KK153402/ESP32_FamicomRomdumper/hardware/Famicom1.kicad_sch

## KiCad design hardware/Famicom1.kicad_sch (2026-09-27)

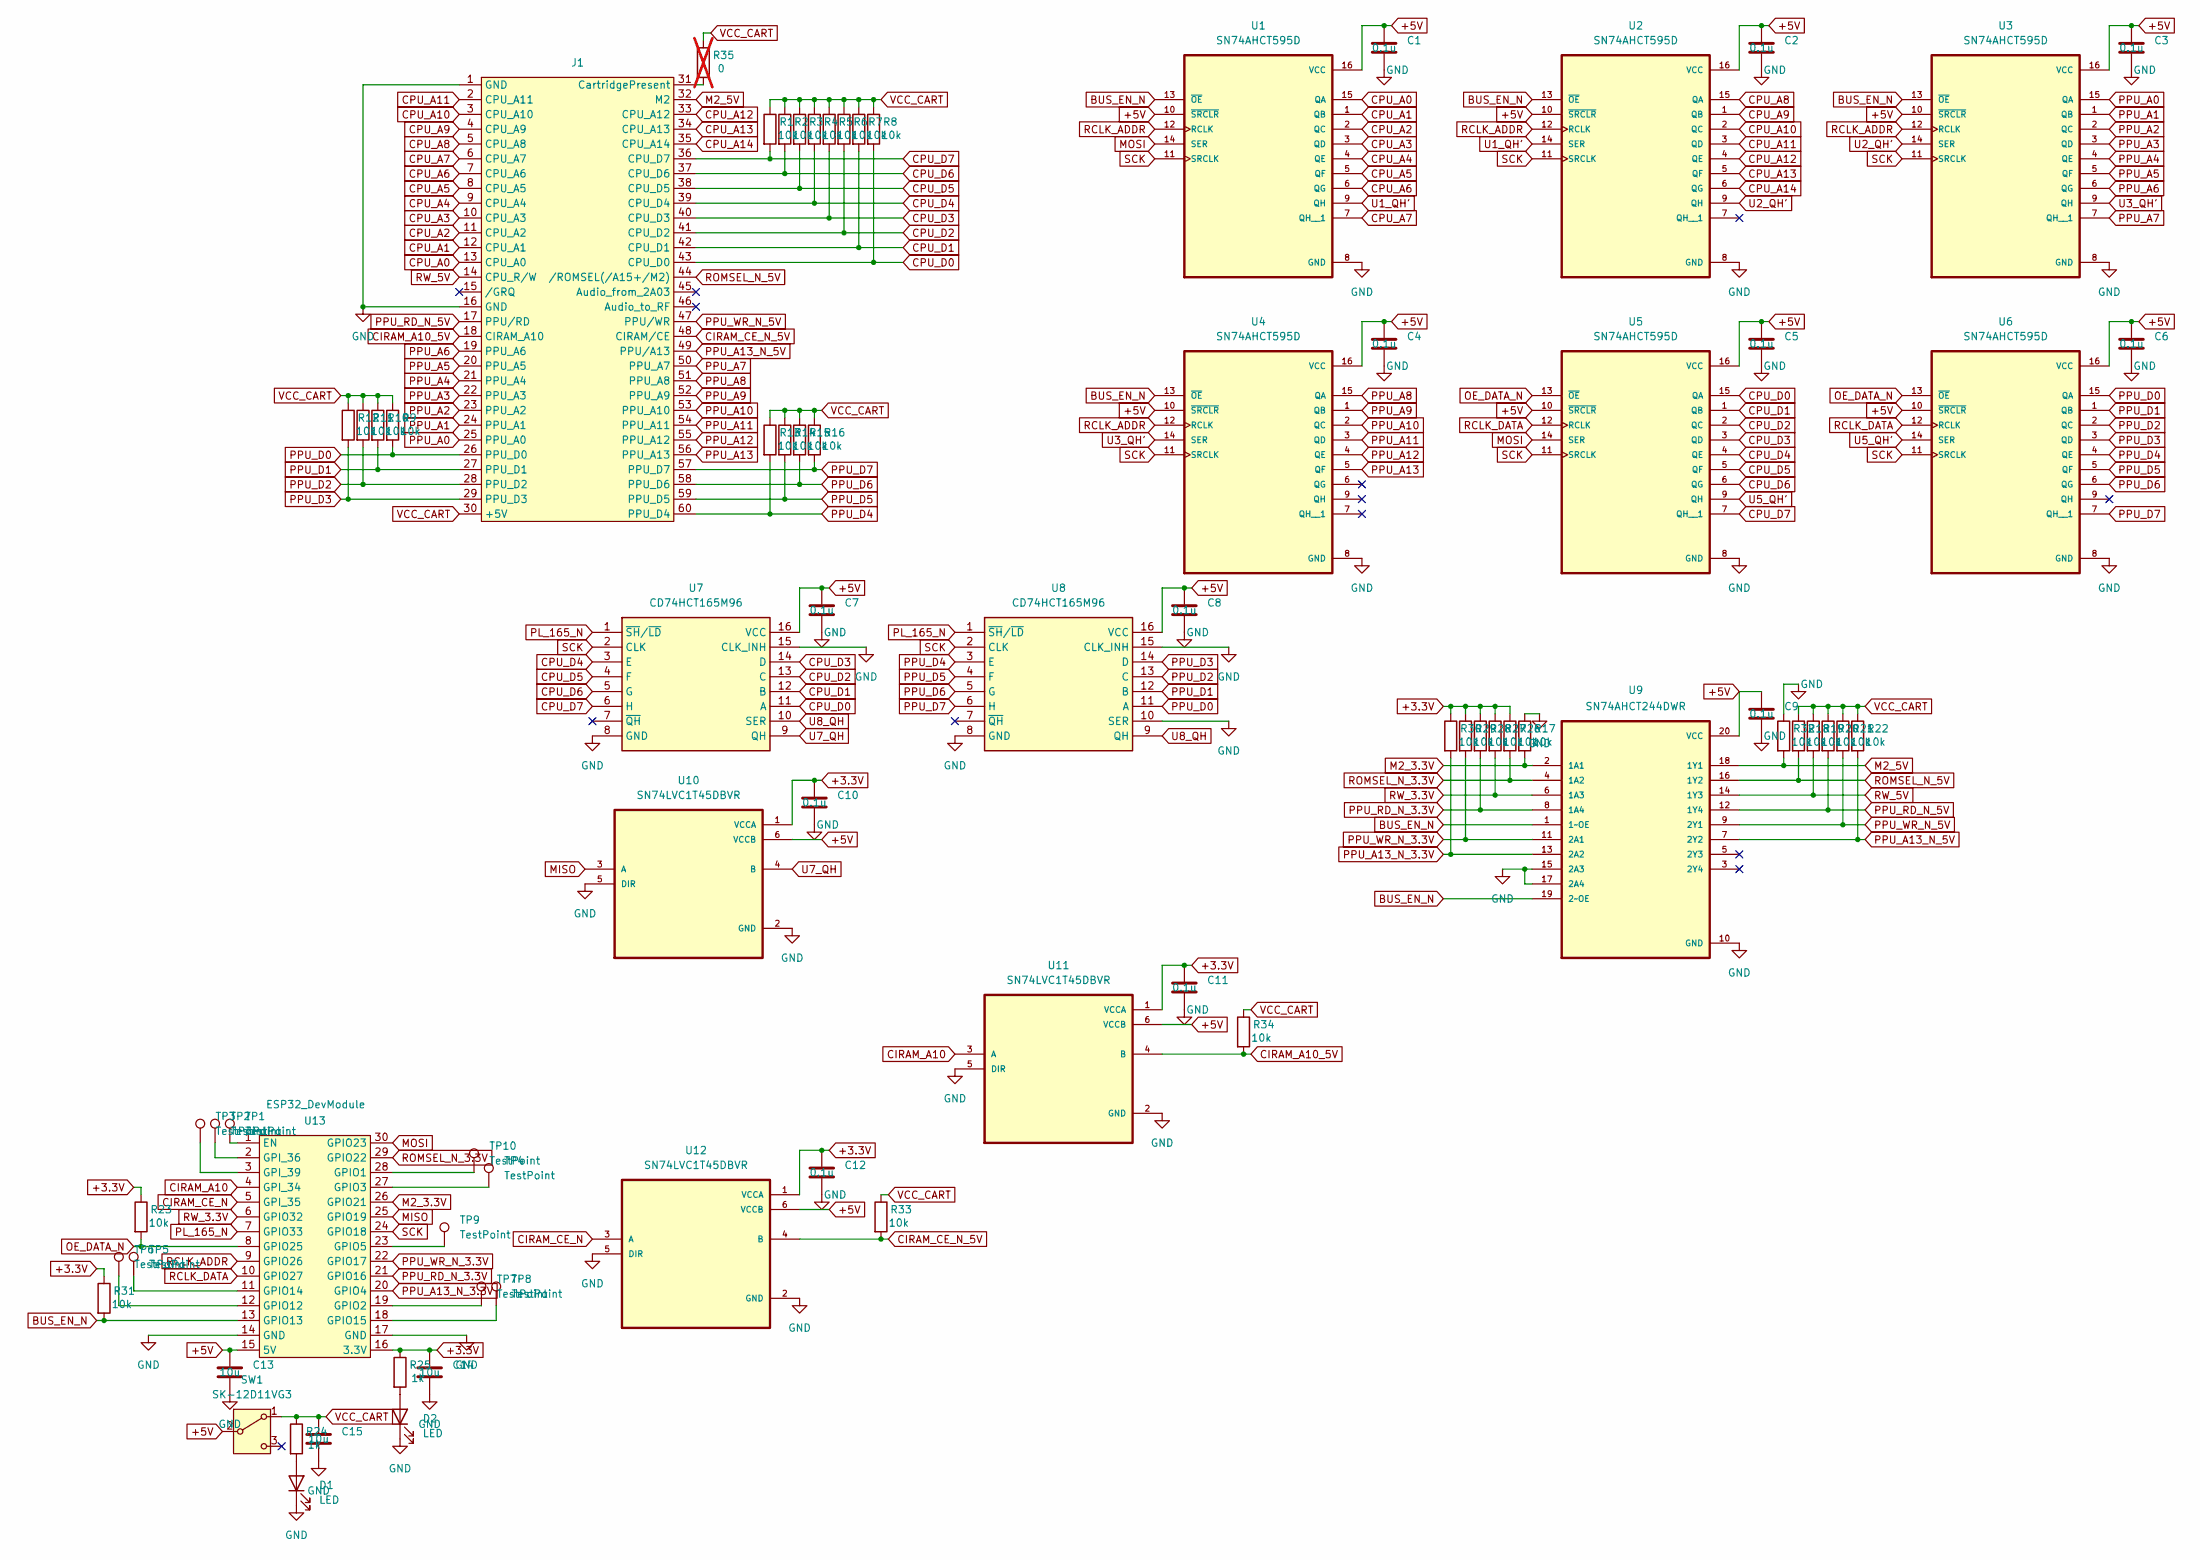
[picture p6: schematic Famicom1.kicad_sch]

Parts:
C1, C2, C3, C4, C5, C6, C7, C8, C9, C10, C11, C12: GRM188F11H104ZA01; C_0603_1608Metric
C13, C14, C15: GRM31CB31H106KA12; C_1206_3216Metric
D1, D2: LED; SML-E12P8WT86
J1: FamilyComputer_60pin
R1, R2, R3, R4, R5, R6, R7, R8, R9, R10, R11, R12, R13, R14, R15, R16, R17, R18, R19, R20, R21, R22, R23, R26, R27, R28, R29, R30, R31, R32, R33, R34: RK73B1JTTD103J; R_0603_1608Metric
R24, R25: RK73B1JTTD102J; R_0603_1608Metric
R35: RK73Z1JTTD; R_0603_1608Metric; not fitted
SW1: SK-12D11VG3
TP1, TP2, TP3, TP4, TP5, TP6, TP7, TP8, TP9, TP10: TestPoint; TestPoint_Pad_2.5x2.5mm
U1, U2, U3, U4, U5, U6: SN74AHCT595D
U7, U8: CD74HCT165M96; Manufacturer_Part_Number CD74HCT165M96; Mouser Part Number 595-CD74HCT165M96
U9: SN74AHCT244DWR
U10, U11, U12: SN74LVC1T45DBVR
U13: ESP32_DevModule

Connections:
+3.3V: C10.1, C11.1, C12.1, C14.1, R23.1, R25.1, R26.1, R27.1, R28.1, R29.1, R30.1, R31.1, U10.1 (VCCA), U11.1 (VCCA), U12.1 (VCCA), U13.16 (3.3V)
+5V: C1.1, C2.1, C3.1, C4.1, C5.1, C6.1, C7.1, C8.1, C9.1, C13.1, SW1.2 (B), U1.10 (~SRCLR), U1.16 (VCC), U2.10 (~SRCLR), U2.16 (VCC), U3.10 (~SRCLR), U3.16 (VCC), U4.10 (~SRCLR), U4.16 (VCC), U5.10 (~SRCLR), U5.16 (VCC), U6.10 (~SRCLR), U6.16 (VCC), U7.16 (VCC), U8.16 (VCC), U9.20 (VCC), U10.6 (VCCB), U11.6 (VCCB), U12.6 (VCCB), U13.15 (5V)
BUS_EN_N: R31.2, U1.13 (~OE), U2.13 (~OE), U3.13 (~OE), U4.13 (~OE), U9.1 (1~OE), U9.19 (2~OE), U13.13 (GPIO13)
CIRAM_A10: U11.3 (A), U13.4 (GPI_34)
CIRAM_A10_5V: J1.18 (CIRAM_A10), R34.2, U11.4 (B)
CIRAM_CE_N: U12.3 (A), U13.5 (GPI_35)
CIRAM_CE_N_5V: J1.48 (CIRAM/CE), R33.2, U12.4 (B)
CPU_A0: J1.13 (CPU_A0), U1.15 (QA)
CPU_A1: J1.12 (CPU_A1), U1.1 (QB)
CPU_A2: J1.11 (CPU_A2), U1.2 (QC)
CPU_A3: J1.10 (CPU_A3), U1.3 (QD)
CPU_A4: J1.9 (CPU_A4), U1.4 (QE)
CPU_A5: J1.8 (CPU_A5), U1.5 (QF)
CPU_A6: J1.7 (CPU_A6), U1.6 (QG)
CPU_A7: J1.6 (CPU_A7), U1.7 (QH__1)
CPU_A8: J1.5 (CPU_A8), U2.15 (QA)
CPU_A9: J1.4 (CPU_A9), U2.1 (QB)
CPU_A10: J1.3 (CPU_A10), U2.2 (QC)
CPU_A11: J1.2 (CPU_A11), U2.3 (QD)
CPU_A12: J1.33 (CPU_A12), U2.4 (QE)
CPU_A13: J1.34 (CPU_A13), U2.5 (QF)
CPU_A14: J1.35 (CPU_A14), U2.6 (QG)
CPU_D0: J1.43 (CPU_D0), R8.2, U5.15 (QA), U7.11 (A)
CPU_D1: J1.42 (CPU_D1), R7.2, U5.1 (QB), U7.12 (B)
CPU_D2: J1.41 (CPU_D2), R6.2, U5.2 (QC), U7.13 (C)
CPU_D3: J1.40 (CPU_D3), R5.2, U5.3 (QD), U7.14 (D)
CPU_D4: J1.39 (CPU_D4), R4.2, U5.4 (QE), U7.3 (E)
CPU_D5: J1.38 (CPU_D5), R3.2, U5.5 (QF), U7.4 (F)
CPU_D6: J1.37 (CPU_D6), R2.2, U5.6 (QG), U7.5 (G)
CPU_D7: J1.36 (CPU_D7), R1.2, U5.7 (QH__1), U7.6 (H)
GND: C1.2, C2.2, C3.2, C4.2, C5.2, C6.2, C7.2, C8.2, C9.2, C10.2, C11.2, C12.2, C13.2, C14.2, C15.2, D1.1 (K), D2.1 (K), J1.1 (GND), J1.16 (GND), R17.1, R32.1, U1.8 (GND), U2.8 (GND), U3.8 (GND), U4.8 (GND), U5.8 (GND), U6.8 (GND), U7.8 (GND), U7.15 (CLK_INH), U8.8 (GND), U8.10 (SER), U8.15 (CLK_INH), U9.10 (GND), U9.15 (2A3), U9.17 (2A4), U10.2 (GND), U10.5 (DIR), U11.2 (GND), U11.5 (DIR), U12.2 (GND), U12.5 (DIR), U13.14 (GND), U13.17 (GND)
M2_3.3V: R17.2, U9.2 (1A1), U13.26 (GPIO21)
M2_5V: J1.32 (M2), R32.2, U9.18 (1Y1)
MISO: U10.3 (A), U13.25 (GPIO19)
MOSI: U1.14 (SER), U5.14 (SER), U13.30 (GPIO23)
unnamed: D1.2 (A), R24.2
unnamed: D2.2 (A), R25.2
unnamed: J1.31 (CartridgePresent), R35.2
unnamed: TP1.1, U13.1 (EN)
unnamed: TP2.1, U13.2 (GPI_36)
unnamed: TP3.1, U13.3 (GPI_39)
unnamed: TP4.1, U13.27 (GPIO3)
unnamed: TP5.1, U13.11 (GPIO14)
unnamed: TP6.1, U13.12 (GPIO12)
unnamed: TP7.1, U13.19 (GPIO2)
unnamed: TP8.1, U13.18 (GPIO15)
unnamed: TP9.1, U13.23 (GPIO5)
unnamed: TP10.1, U13.28 (GPIO1)
OE_DATA_N: R23.2, U5.13 (~OE), U6.13 (~OE), U13.8 (GPIO25)
PL_165_N: U7.1 (~SH/~LD), U8.1 (~SH/~LD), U13.7 (GPIO33)
PPU_A0: J1.25 (PPU_A0), U3.15 (QA)
PPU_A1: J1.24 (PPU_A1), U3.1 (QB)
PPU_A2: J1.23 (PPU_A2), U3.2 (QC)
PPU_A3: J1.22 (PPU_A3), U3.3 (QD)
PPU_A4: J1.21 (PPU_A4), U3.4 (QE)
PPU_A5: J1.20 (PPU_A5), U3.5 (QF)
PPU_A6: J1.19 (PPU_A6), U3.6 (QG)
PPU_A7: J1.50 (PPU_A7), U3.7 (QH__1)
PPU_A8: J1.51 (PPU_A8), U4.15 (QA)
PPU_A9: J1.52 (PPU_A9), U4.1 (QB)
PPU_A10: J1.53 (PPU_A10), U4.2 (QC)
PPU_A11: J1.54 (PPU_A11), U4.3 (QD)
PPU_A12: J1.55 (PPU_A12), U4.4 (QE)
PPU_A13: J1.56 (PPU_A13), U4.5 (QF)
PPU_A13_N_3.3V: R30.2, U9.13 (2A2), U13.20 (GPIO4)
PPU_A13_N_5V: J1.49 (PPU/A13), R22.2, U9.7 (2Y2)
PPU_D0: J1.26 (PPU_D0), R9.2, U6.15 (QA), U8.11 (A)
PPU_D1: J1.27 (PPU_D1), R10.2, U6.1 (QB), U8.12 (B)
PPU_D2: J1.28 (PPU_D2), R11.2, U6.2 (QC), U8.13 (C)
PPU_D3: J1.29 (PPU_D3), R12.2, U6.3 (QD), U8.14 (D)
PPU_D4: J1.60 (PPU_D4), R13.2, U6.4 (QE), U8.3 (E)
PPU_D5: J1.59 (PPU_D5), R14.2, U6.5 (QF), U8.4 (F)
PPU_D6: J1.58 (PPU_D6), R15.2, U6.6 (QG), U8.5 (G)
PPU_D7: J1.57 (PPU_D7), R16.2, U6.7 (QH__1), U8.6 (H)
PPU_RD_N_3.3V: R28.2, U9.8 (1A4), U13.21 (GPIO16)
PPU_RD_N_5V: J1.17 (PPU/RD), R20.2, U9.12 (1Y4)
PPU_WR_N_3.3V: R29.2, U9.11 (2A1), U13.22 (GPIO17)
PPU_WR_N_5V: J1.47 (PPU/WR), R21.2, U9.9 (2Y1)
RCLK_ADDR: U1.12 (RCLK), U2.12 (RCLK), U3.12 (RCLK), U4.12 (RCLK), U13.9 (GPIO26)
RCLK_DATA: U5.12 (RCLK), U6.12 (RCLK), U13.10 (GPIO27)
ROMSEL_N_3.3V: R26.2, U9.4 (1A2), U13.29 (GPIO22)
ROMSEL_N_5V: J1.44 (/ROMSEL(/A15+/M2)), R18.2, U9.16 (1Y2)
RW_3.3V: R27.2, U9.6 (1A3), U13.6 (GPIO32)
RW_5V: J1.14 (CPU_R/W), R19.2, U9.14 (1Y3)
SCK: U1.11 (SRCLK), U2.11 (SRCLK), U3.11 (SRCLK), U4.11 (SRCLK), U5.11 (SRCLK), U6.11 (SRCLK), U7.2 (CLK), U8.2 (CLK), U13.24 (GPIO18)
U1_QH': U1.9 (QH), U2.14 (SER)
U2_QH': U2.9 (QH), U3.14 (SER)
U3_QH': U3.9 (QH), U4.14 (SER)
U5_QH': U5.9 (QH), U6.14 (SER)
U7_QH: U7.9 (QH), U10.4 (B)
U8_QH: U7.10 (SER), U8.9 (QH)
VCC_CART: C15.1, J1.30 (+5V), R1.1, R2.1, R3.1, R4.1, R5.1, R6.1, R7.1, R8.1, R9.1, R10.1, R11.1, R12.1, R13.1, R14.1, R15.1, R16.1, R18.1, R19.1, R20.1, R21.1, R22.1, R24.1, R33.1, R34.1, R35.1, SW1.1 (A)
